QuentiumYT/TimeToEat/images/20181215_115844.jpg

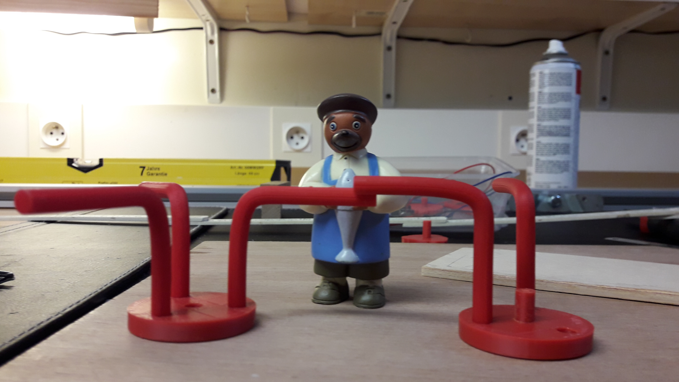
images/20181215_115844.jpg
