QuentiumYT/TimeToEat/images/20181215_132538.jpg

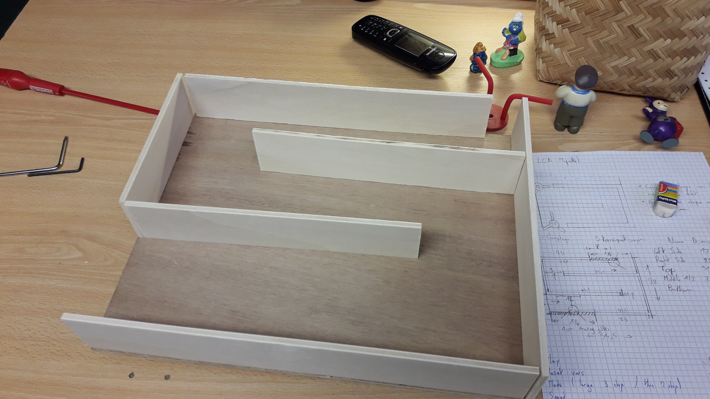
images/20181215_132538.jpg
