QuentiumYT/TimeToEat/images/20181215_132542.jpg

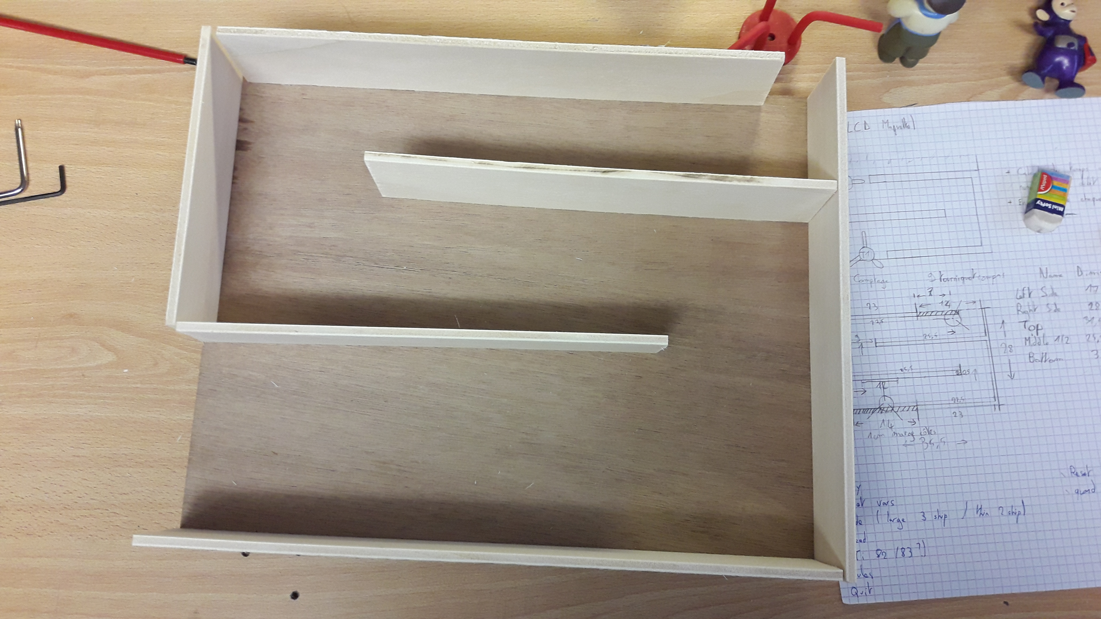
images/20181215_132542.jpg
