QuentiumYT/TimeToEat/images/20181215_135226.jpg

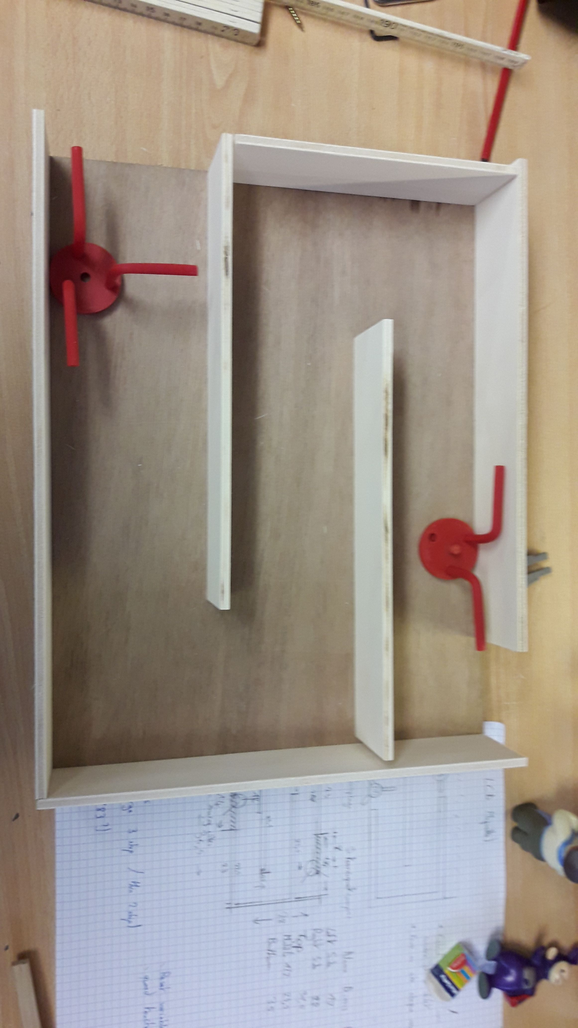
images/20181215_135226.jpg
