QuentiumYT/TimeToEat/images/20181215_135229.jpg

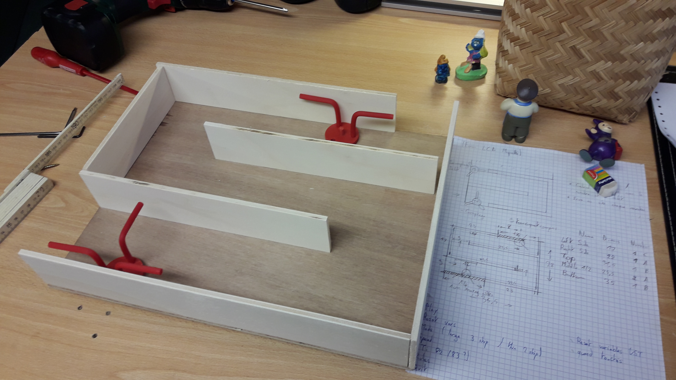
images/20181215_135229.jpg
