QuentiumYT/TimeToEat/images/20181215_152853.jpg

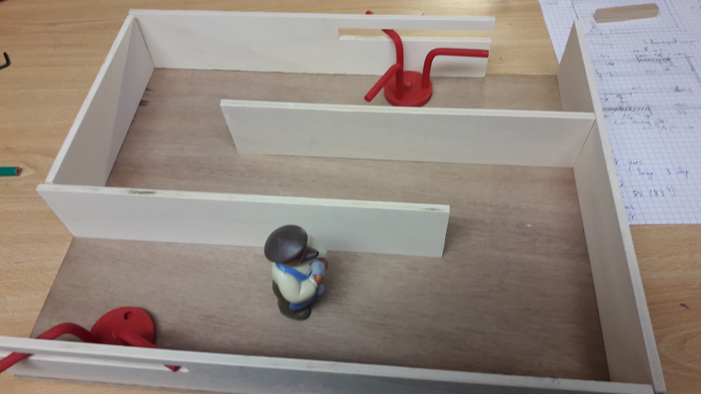
images/20181215_152853.jpg
