QuentiumYT/TimeToEat/images/20181215_152859.jpg

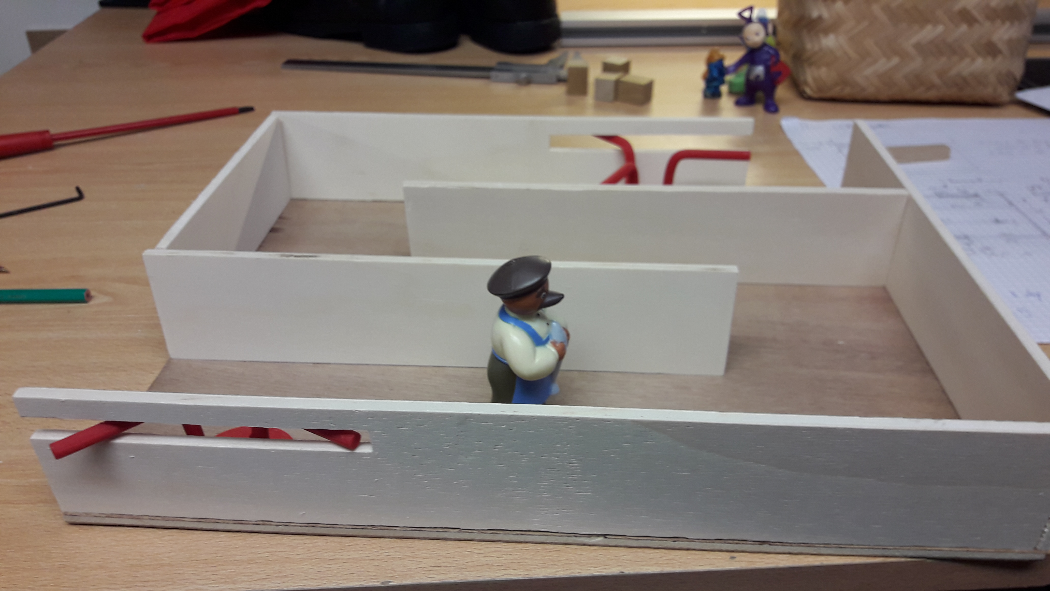
images/20181215_152859.jpg
