QuentiumYT/TimeToEat/images/20190205_115815.jpg

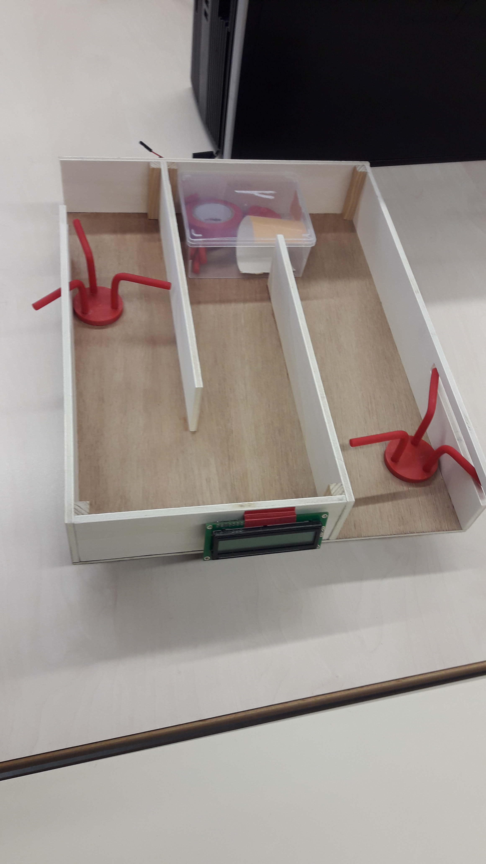
images/20190205_115815.jpg
