QuentiumYT/TimeToEat/images/20190205_115823.jpg

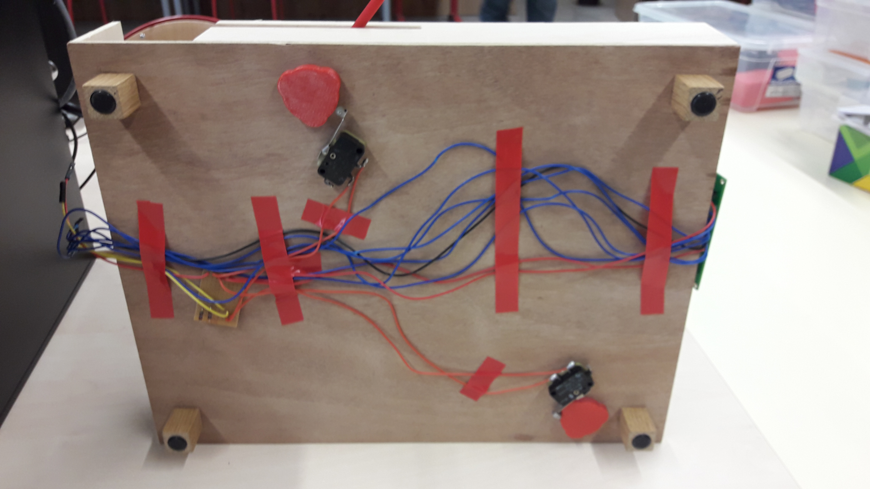
images/20190205_115823.jpg
