QuentiumYT/TimeToEat/images/20190305_111720.jpg

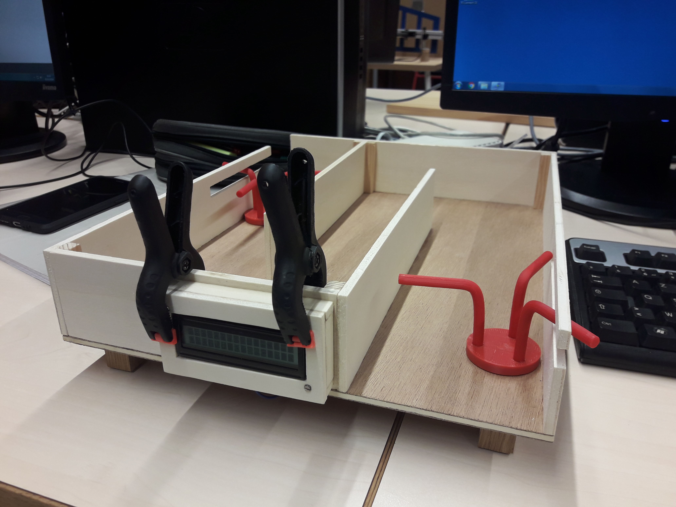
images/20190305_111720.jpg
