QuentiumYT/TimeToEat/images/20190305_111722.jpg

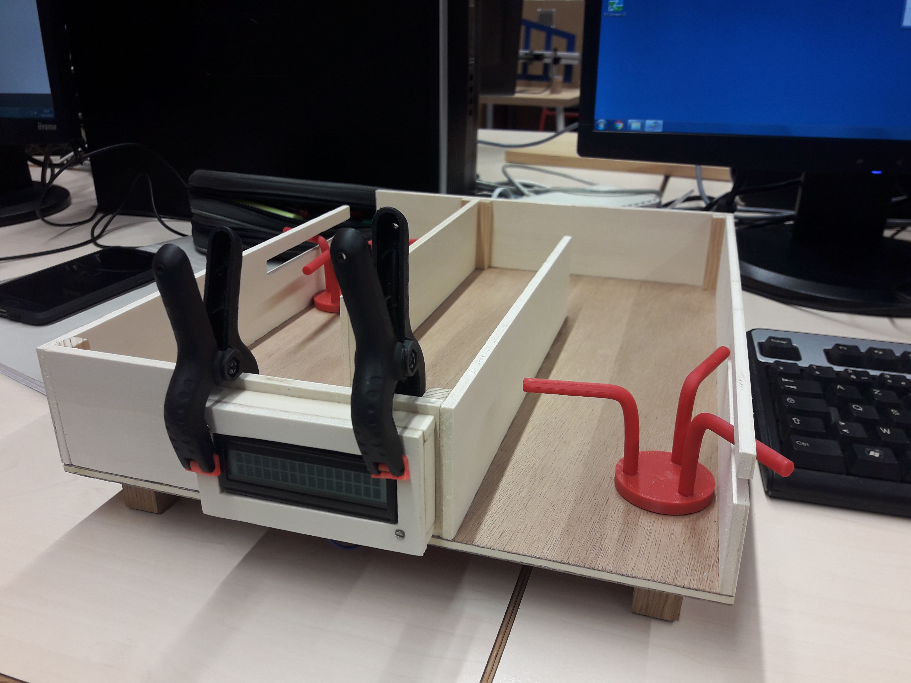
images/20190305_111722.jpg
