QuentiumYT/TimeToEat/images/20190305_111728.jpg

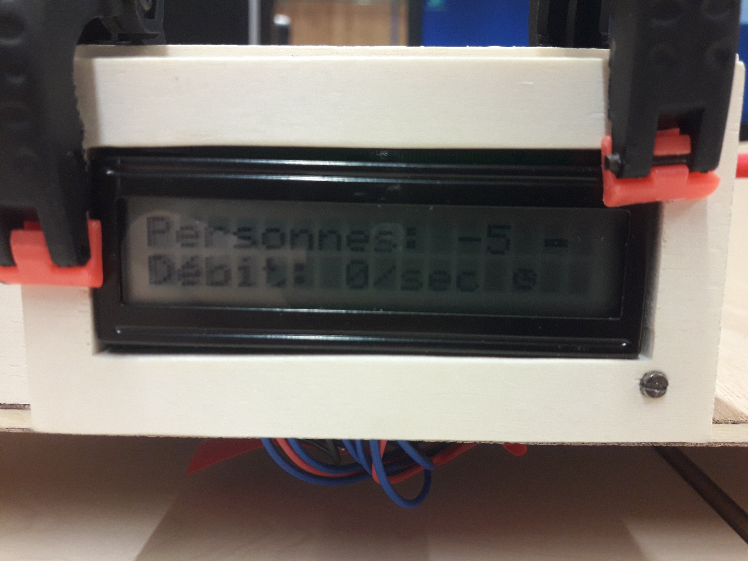
images/20190305_111728.jpg
