QuentiumYT/TimeToEat/images/20190503_141344.jpg

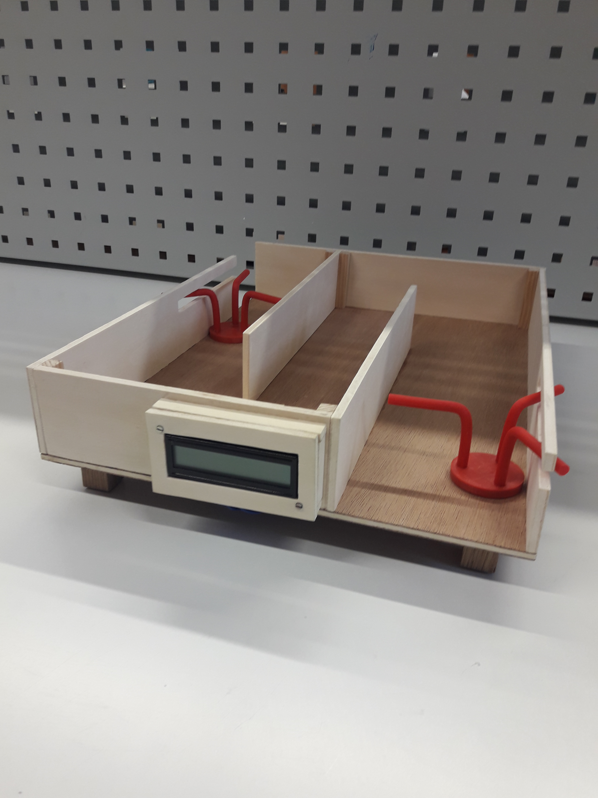
images/20190503_141344.jpg
