QuentiumYT/TimeToEat/images/20190503_141351.jpg

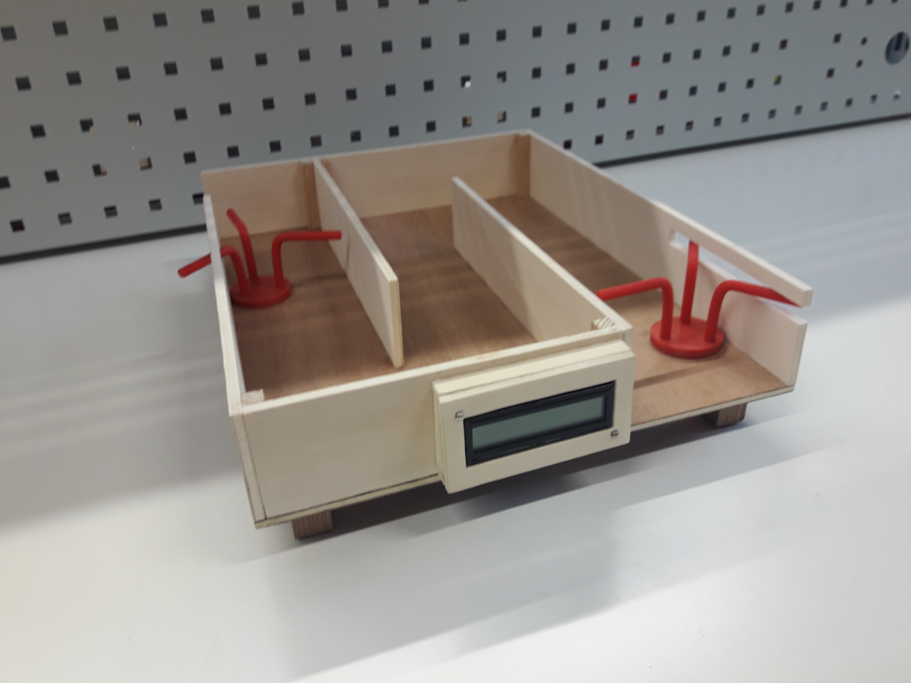
images/20190503_141351.jpg
