QuentiumYT/TimeToEat/images/20190503_141352.jpg

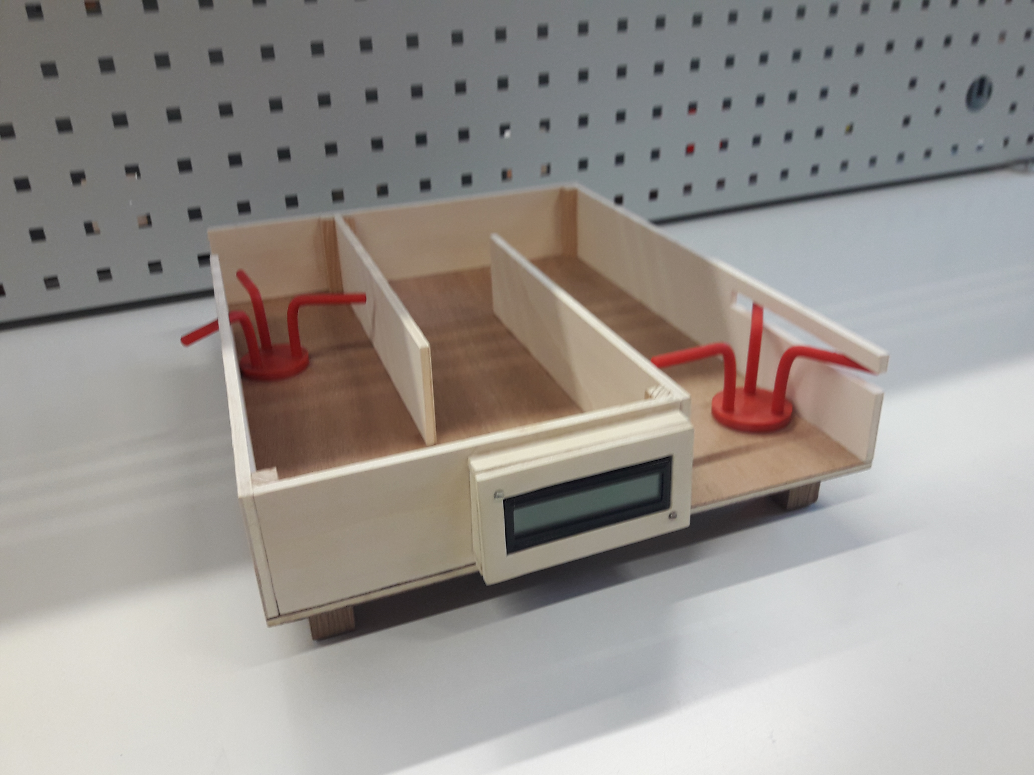
images/20190503_141352.jpg
