QuentiumYT/TimeToEat/images/Temps réel 1.png

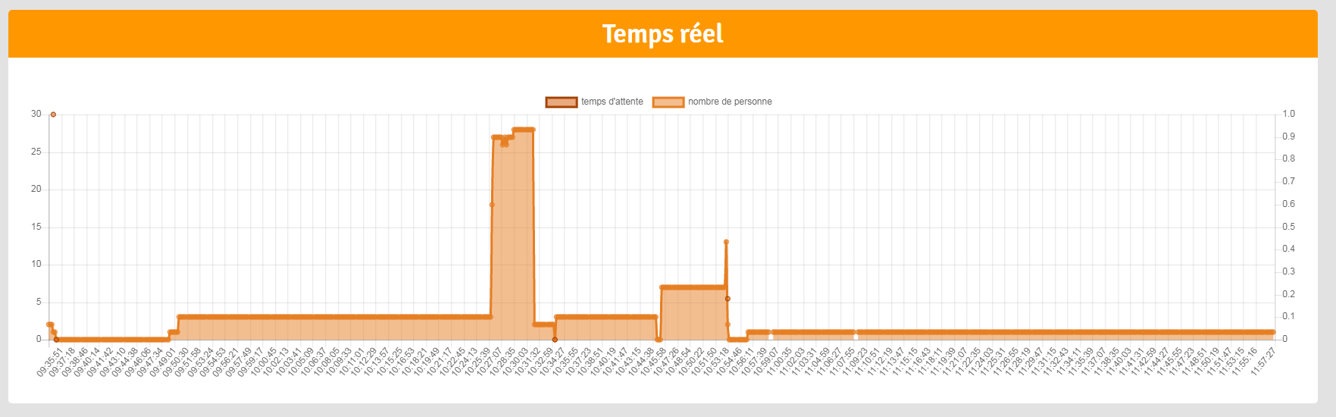
images/Temps réel 1.png
