QuentiumYT/TimeToEat/raspberry/pip_freeze.png

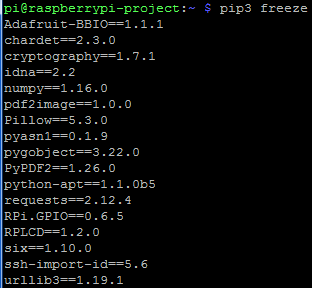
raspberry/pip_freeze.png
