QuentiumYT/TimeToEat/rerun_project/TimeToEat_Brooch.png

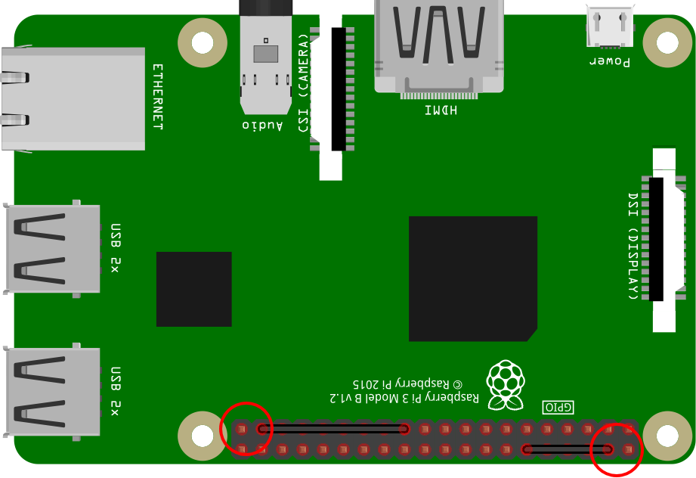
rerun_project/TimeToEat_Brooch.png
