QuentiumYT/TimeToEat/web/img/arrow_left.png

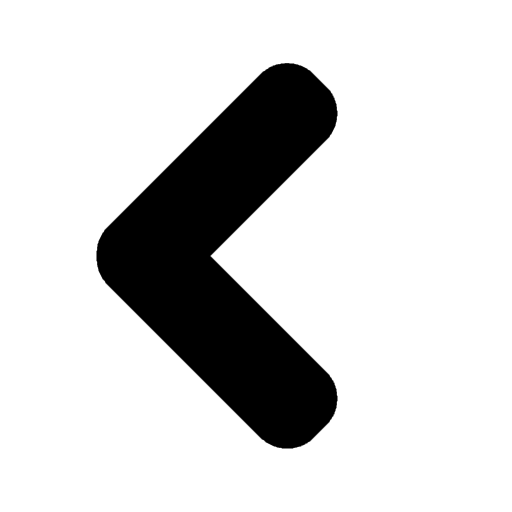
web/img/arrow_left.png
