QuentiumYT/TimeToEat/web/img/tahina.jpg

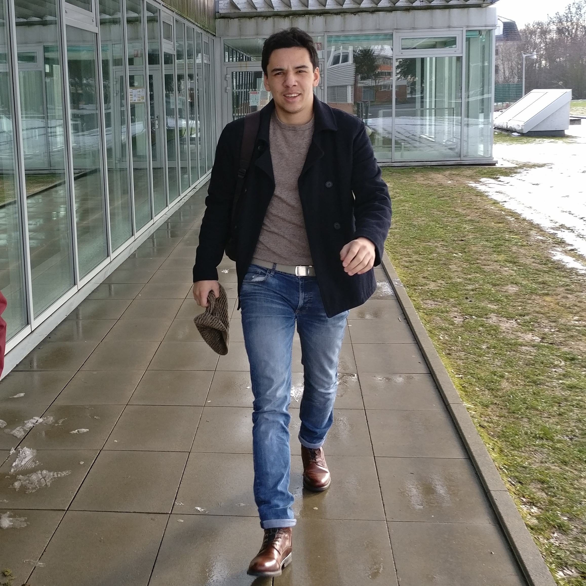
web/img/tahina.jpg
