QuentiumYT/TimeToEat/rerun_project/TimeToEat_Wiring.png

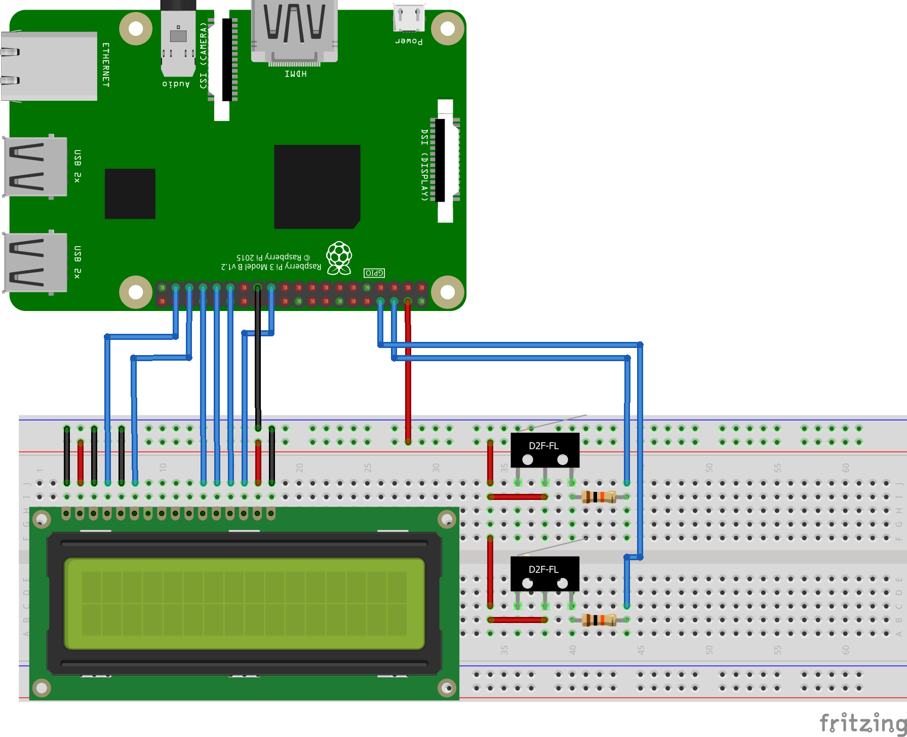
rerun_project/TimeToEat_Wiring.png
